tombueng/LuxDMX/docs/display.md

# Design — OLED / TFT status display (issue #5)

Add an **optional on-device display** that shows the gateway's live status without a
browser — IP, universe, frame rate, source count, link quality, and DMX activity —
and **auto-rotates to an alert banner** when something needs attention (two consoles
fighting over the universe, identify, manual override).

> Status: **implemented & committed** on the `hardware` branch (all four firmware envs build).
> Mono bring-up panels ordered: Retoo SH1106 128×64, ARCELI SSD1306 128×64, MakerHawk SSD1306
> 128×32 — covers `dispType 1/2/3`. Colour/SPI path (`dispType 4`) is built but on-hardware
> verification is pending a panel (an SSD1351, or a TFT added per §7 on an existing display).

---

## 1. Displays we support & the graphics library

Two display classes, **one drawing API**:

| Class | Controllers | Bus | Pins | Buffer | Boards |
|---|---|---|---|---|---|
| **Mono OLED** | SSD1306 (128×64, 128×32), SH1106 (128×64) | I²C | 2 | 1 KB | all four |
| **Color OLED** | SSD1351 (128×128 RGB) | SPI | ~5 | 32 KB canvas | esp32 / esp32-s3 only |
| Color TFT *(§7, later)* | ST7735 / ST7789 / ILI9341 | SPI | ~5 | direct-draw | esp32 / esp32-s3 only |

**Library: the [Adafruit_GFX](https://github.com/adafruit/Adafruit-GFX-Library) family**
(not U8g2). Every driver below derives from the common `Adafruit_GFX` base, so the renderer
draws once through a single `Adafruit_GFX*` pointer with `uint16_t` RGB565 colors — monochrome
panels map any non-black color to "pixel on," the SSD1351 shows real color:

```
olikraus/U8g2          ✗  (drives SSD1351 only in monochrome — defeats the color panel)
adafruit/Adafruit GFX Library          ← base class + fonts
adafruit/Adafruit SSD1306              ← SSD1306 mono I²C   (dispType 1,2)
adafruit/Adafruit SH110X               ← SH1106  mono I²C   (dispType 3)  ← Retoo panel
adafruit/Adafruit SSD1351 OLED Library ← SSD1351 color SPI  (dispType 4)  ← DollaTek panel
```

Why this over U8g2: it's the only option that drives **both** the mono I²C OLED *and* a
**full-color** SSD1351 with **one** rendering routine, it opens the §7 color-TFT path for free,
and it matches the Adafruit ecosystem the firmware already uses (`Adafruit_NeoPixel`). Trade-off
vs U8g2: no page-buffer low-RAM mode (mono keeps a 1 KB buffer — fine; we already gate WS push
under 40 KB heap) and a smaller built-in font set (ample for a status screen).

```cpp
Adafruit_GFX* gfx = nullptr;   // draw target: device buffer (mono) or GFXcanvas16 (colour)
// flush: mono -> dispDev->display();  colour -> dispDev->drawRGBBitmap(canvas->getBuffer())
// factory (initDisplay):
//   case 1: gfx = dispDev = new Adafruit_SSD1306(128,64,&Wire,-1); ->begin(...,/*periphBegin*/false);
//   case 3: gfx = dispDev = new Adafruit_SH1106G(128,64,&Wire,-1); ->begin(addr,true);
//   case 4: SPI.begin(sck,-1,mosi,cs); dispDev = new Adafruit_SSD1351(128,128,&SPI,cs,dc,rst);
//           dispDev->begin();  gfx = dispCanvas = new GFXcanvas16(128,128);
```

The per-type `begin()` / flush differences live in the factory; the renderer is type-agnostic.

---

## 2. Pin availability

Mono I²C needs **2 bidirectional GPIOs** (input-only 34–39 can't drive SDA/SCL). Color OLED /
TFT over SPI needs **~5** (SCK, MOSI, CS, DC, RST).

| Board | DMX / LED / EN | Eaten by Ethernet | Free output-capable | Mono I²C | Color SPI |
|---|---|---|---|:--:|:--:|
| `esp32dev` (WROOM) | 16/17, LED 2 | — | 21, 22 (+ many) | ✓ | ✓ (HW SPI 18/23 + CS/DC/RST) |
| `esp32s3dev` | 16/17, LED 48 | — | abundant | ✓ | ✓ |
| `wt32eth01` | 4/5, LED 2 | 0,16,18,19,21,22,23,25,26,27 | **14, 15, 17** only | ✓ | ✗ |
| carrier / `esp32-poe-iso` | 4/36, EN 32, RGB 33 | 0,12,18,19,21,22,23,25,26,27 | 5, 13, 14, 15, 16 | ✓ | ✗ (needs all 5 spares) |

**The color SSD1351 runs on the WiFi dev boards (where bring-up happens), not the Ethernet
boards.** The mono Retoo panel runs everywhere.

**Strapping cautions** (baked into defaults + form help): avoid **GPIO12** (boot-straps flash
voltage; an OLED pull-up can brick boot); **GPIO15** is fine pulled high; on **WT32-ETH01
GPIO16 is the PHY-power pin** — off-limits there.

### Recommended default pins (compile-time `DEF_DISP_*`, overridable in `/config`)

| Board | I²C SDA | I²C SCL |
|---|---|---|
| `esp32dev` | 21 | 22 |
| `esp32s3dev` | 8 | 9 |
| `wt32eth01` | 14 | 15 |
| carrier / `esp32-poe-iso` | 13 | 16 |

Color-SPI pins have no universal default (they're board-specific and only used for `dispType 4`)
— the user sets CS/DC/RST/SCK/MOSI in `/config`. Default `dispType = 0` (**off**) everywhere, so
existing units are unaffected until a user opts in.

---

## Header safety: J4 vs J6

The LuxDMX board has **two** JST SH 1.0 mm 9-pin headers next to each other: **J4** (display) and
**J6** (expansion). Same connector, so a cable physically plugs into either one.

Both headers carry the **same power pins**, and a hard validator
(`hardware/scripts/validate_header_parity.py`) fails the fab export if that ever stops being true:

| pin | J4 — display | J6 — expansion |
|---|---|---|
| **1** | **+3V3** | **+3V3** |
| **2** | **GND** | **GND** |
| 3 | SDA (IO4) | IO35 |
| 4 | SCL (IO5) | IO36 |
| 5 | SCK (IO39) | IO37 |
| 6 | MOSI (IO40) | IO48 |
| 7 | CS (IO41) | TX0 (IO43) |
| 8 | DC (IO42) | RX0 (IO44) |
| 9 | RST (IO38) | GND |

Get it wrong and nothing breaks. The panel still receives correct power; only 3V3 CMOS signals land
in the wrong places, which both sides tolerate. A display plugged into J6 lands its RST on GND, so it
sits harmlessly in reset — dark, but fine. Move it to J4 and it comes up.

**There is no +5V on J6.** Anything needing 5 V gets it from your own supply. That is deliberate:
sharing one power layout across both headers is what makes a swapped cable a non-event, and there
was no free non-strapping GPIO left for a 7th signal anyway (IO3/IO45/IO46 are all strapping), so
pin 9 became a second ground instead.

Labelling the two cables is still worth the ten seconds — a strip of tape saying `DISP` / `EXP` is
what you'll actually read at 2am during a show. And if you only ever use one, **populate only J4**
and leave J6 unfitted.

---

## 3. Config keys

Mirrors how the status LED is wired through the stack (`ledType`/`ledPin`).

| `Config` field | NVS key | `/config` field | Range | Default | Used by |
|---|---|---|---|---|---|
| `dispType` | `disptype` | select | 0=off · 1=SSD1306 128×64 · 2=SSD1306 128×32 · 3=SH1106 128×64 · **4=SSD1351 128×128 color** | `0` | all |
| `dispSda` | `dispsda` | number | −1..48 | `DEF_DISP_SDA` | I²C (1–3) |
| `dispScl` | `dispscl` | number | −1..48 | `DEF_DISP_SCL` | I²C (1–3) |
| `dispRot` | `disprot` | select | 0=normal · 1=flipped 180° | `0` | all |
| `dispCs` | `dispcs` | number | −1..48 | −1 | SPI (4) |
| `dispDc` | `dispdc` | number | −1..48 | −1 | SPI (4) |
| `dispRst` | `disprst` | number | −1..48 | −1 | SPI (4) |
| `dispSck` | `dispsck` | number | −1..48 | −1 | SPI (4) |
| `dispMosi` | `dispmosi` | number | −1..48 | −1 | SPI (4) |

- **I²C address** isn't a field — `initDisplay()` probes `0x3C` then `0x3D` and logs which
  answered. (SSD1351 ignores it.)
- The `/config` "Display" card shows the **I²C pin rows for types 1–3** and the **SPI pin rows
  for type 4**, toggled in JS by the selected type (like `updLedPin()`).
- Touchpoints (all following the LED pattern): `loadConfig` / `saveConfig`, `handleConfigPost`,
  `handleInfoJson`, `src/pages/config.html`.
- **Phase 1 status:** `dispType` (0–3), `dispSda`, `dispScl`, `dispRot` are built and compiling.
  The SPI keys + `dispType 4` are added when color support lands (Phase 2).

---

## 4. Architecture — a `displayTask`, like `ledTask`

The display renders on its **own low-priority FreeRTOS task** (≈4 Hz), exactly like
[`ledTask`](../src/main.cpp). It only **reads** existing state snapshots (`fps`, `senders`,
`netLocalIP()`, `cfg.*`, `hasConflict()`, `manualMode`, `identifyCh`, `dmxBuf`) — never touches
the DMX UART, never blocks `loop()`. A mono I²C flush is ~10–30 ms at 400 kHz; an SSD1351
partial-region redraw over SPI is a few ms — both safely off the DMX path.

```
setup():  loadConfig() → initDisplay() [splash]  →  xTaskCreate(displayTask, "disp", 4096, …, 1)
displayTask():  pick screen (priority, §5) → render via Adafruit_GFX* → flush → delay(250 ms)
```

- `initDisplay()` is a no-op when `dispType == 0`; on probe/begin failure it logs and leaves
  `gfx == nullptr` (no hang — I²C `begin()` NAK-times out; SPI begin always returns).
- Boot sequence on the panel: **"LuxDMX vX.Y.Z"** splash → **"Connecting…"** → status once
  `netConnected()`.
- Color path is **double-buffered**: the renderer draws into a `GFXcanvas16` (32 KB, allocated
  only when `dispType == 4`) and `dispFlush()` blits the whole frame with one `drawRGBBitmap()`.
  The SSD1351 has no RAM buffer, so without this it would visibly flicker — clearing then
  redrawing live on the SPI bus. Mono panels buffer internally, so they flush with `display()`.

---

## 5. Screens — status + auto-rotate

One **status screen** is the resting state. The task switches to a full-screen **alert banner**
while a condition is active, then falls back. No button required.

**Priority (first active wins):** `hasConflict()` → `IDENTIFY` → `manualMode` → status.
Banners dwell ≥1.5 s so a brief blip stays readable.

### 128×64 mono / 128×128 color (8 rows)

Single output (resting):

```
┌────────────────────────────┐
│ LuxDMX           1.0.42  │  title + FIRMWARE_VERSION
│ 192.168.1.50               │  netLocalIP()  — the #1 walk-up info
│ Uni 0    Both              │  output universe + protocol
│ In 33 Out 40 C     Src 1   │  inFpsLive/outFpsLive + style tag
│ WiFi -47dBm         ● LIVE │  link dBm (or "ETH up") + DMX live/idle
└────────────────────────────┘
```

With **both outputs enabled** the universe + FPS rows split into one row per output, each
showing its own universe and its own frame rate (source count moves to the right):

```
┌────────────────────────────┐
│ LuxDMX           1.0.42  │
│ 192.168.1.50               │
│ A U0 44.0fps C             │  output A: universe + out fps + style
│ B U5 43.8fps C      Src 1  │  output B + activeSenderCount()
│ WiFi -47dBm         ● LIVE │
└────────────────────────────┘
```

- Link row: WiFi shows dBm (`netRSSI()`); Ethernet shows `ETH up/down`.
- Universe(s): `dispUniverseLabel()` joins every **enabled** output's universe (`0`, or `0+5`
  for two) in the single-output layout; with two outputs each gets its own `A`/`B` row.
- Per-output FPS: `dispOutFps(i)` is each universe's own 1 s frame rate, and reads `0.0` once
  that input stalls (>1.5 s). The aggregate `fps` still feeds the WebSocket / web UI.
- Rate and style (issue #93): the single-output rows show **In** and **Out** side by side
  rather than one ambiguous `FPS`, because the whole point is whether the two match. A
  trailing `C` or `D` is the transmit style of that port, continuous (free-running at the
  configured rate) or delta (one frame out per frame in). `In 33 Out 40 C` says at a glance
  that this port is resampling a 33.3 fps console onto a 40 fps wire and therefore repeating
  roughly one frame in six.
- Source count: labelled **Sources** (number of active Art-Net / sACN senders), matching the
  `2+ sources` wording on the conflict banner.
- DMX state: `● LIVE` when `millis() - lastDmxMs < 1500` (the LED's threshold), else `idle`.
- **Color panel (SSD1351)** reuses the device's status palette, same language as the status LED:
  title accent + LIVE dot **green** when up (idle *or* live — the LIVE/idle label carries the DMX
  distinction), **orange** when Ethernet is configured but running on the WiFi/AP fallback,
  **blue** during RDM / identify, **red** on no-link; the conflict banner fills **red**. Panel and
  LED always agree.

> **Mono panel color is irrelevant.** White / blue / yellow / yellow-blue panels are all 1 bpp —
> the color is the physical emitter, not addressable. The yellow/blue split panel has a *fixed*
> divide (top 16 px yellow, rest blue) with a small dead gap at y=16; the 64-px layout puts the
> title in y=0..15 (the yellow band) and keeps the first data row at y≥18 so nothing straddles
> the gap. Split panels are 128×64 only.

### 128×32 mono (4 rows)

Title + RSSI bars dropped; live dot moves up beside the IP:

```
┌────────────────────────────┐
│ 10.13.37.2          ● LIVE │
│ U0+5 Both                  │
│ 44.0C/43.8C Src 1          │  per-output out fps + style tag
└────────────────────────────┘
```

The renderer branches on `gfx->height()`, so the same data helpers feed every layout; banners
reuse one centred-text routine with a font chosen by height. **Why size/type is configured, not
detected:** over I²C both heights answer at 0x3C with no resolution read-back, and SPI panels
can't be enumerated at all — so the panel is part of `dispType`, picked in `/config`.

### Controls menu (issue #24)

If a rotary encoder or buttons are wired (see [controls.md](controls.md)), a highest-priority
menu screen takes over the display while you're navigating: a scrolling item list on the tall
panels, or the single selected item on the 128×32 strip. A `>` caret marks the highlight (the
only cue that survives the 1-bit mono collapse), and editing a value wraps it in `<angle
brackets>`. It shows instantly on the first turn and disappears the moment the menu closes.

### Future extra screens (not in v1)

Button-cycled diagnostics — DMX mini-bargraph, RDM device count (`rdmCount`), uptime/heap. The
screen-selector enum is built to extend.

---

## 6. platformio.ini changes

```ini
[env]                       # add to shared lib_deps
lib_deps =
    …
    adafruit/Adafruit GFX Library @ ^1.11.11
    adafruit/Adafruit SSD1306     @ ^2.5.13
    adafruit/Adafruit SH110X      @ ^2.1.12
    adafruit/Adafruit SSD1351 OLED Library @ ^1.3.2

[env:esp32dev]    build_flags = … -DDEF_DISP_SDA=21 -DDEF_DISP_SCL=22
[env:esp32s3dev]  build_flags = … -DDEF_DISP_SDA=8  -DDEF_DISP_SCL=9
[env:wt32eth01]   build_flags = … -DDEF_DISP_SDA=14 -DDEF_DISP_SCL=15
```

`dispType` stays `0` by default in all envs; the user enables the panel from `/config`.

---

## 7. Color TFT — later (esp32 / esp32-s3 only)

Same `Adafruit_GFX*` renderer, additional `dispType` values for `ST7735 160×128` /
`ST7789 240×240` / `ILI9341 320×240` behind their Adafruit drivers, reusing the same SPI pin
config keys from §3. The color SSD1351 work lands most of this — TFT is then just more driver
cases + a larger-font layout. Out of scope for issue #5's first cut.

---

## 8. Verification plan

- **Hardware**: the **Retoo SH1106** on `esp32dev`/`esp32s3dev` (I²C 21/22 or 8/9) → mono path,
  address probe, rotation; the **DollaTek SSD1351** on SPI → color path, status palette; trigger
  the conflict banner by pointing two Art-Net sources at one universe.

---

## 9. Build phases — all implemented

1. ✅ Config plumbing — `Config` fields, NVS, `handleConfigPost`, `handleInfoJson`, `/config`
   "Display" card + JS; `/info.json` round-trips `dispType` + I²C/SPI pins + rotation.
2. ✅ Adafruit_GFX family; `initDisplay()` factory + I²C probe (bails if no panel) + DC-pin guard
   + boot splash; `dispType 4` (SSD1351) with a `GFXcanvas16` double-buffer; per-board `DEF_DISP_*`.
3. ✅ `displayTask()` + status screen (height-aware 128×32 / 128×64 / 128×128 hero layouts).
4. ✅ Auto-rotate banners (conflict / identify / manual) with priority + dwell; colour status palette.
5. ✅ README "Display" section + rendered `display-preview.png`.

**Remaining:** on-hardware bring-up of the mono panels and the colour/SPI path; optional §7 TFT
support (verify colour/SPI on an existing TFT instead of buying an SSD1351).
