tombueng/LuxDMX/web/boards/CREDITS.md

# Board diagram credits

The `/config` pin picker draws a **generated horizontal diagram** for every board
straight from the descriptor's pin data. There are **no third-party image assets** in
this catalog: no board photos and no Fritzing/realistic graphics. Every diagram is our
own SVG, drawn in the browser from the board's GPIO columns.

The GPIO data behind each diagram comes from:

| Board(s) | Source | License |
|---|---|---|
| LuxDMX v6 | the PCB netlist (`hardware/scripts/luxdmx.py`) | project (MIT) |
| ESP32 DevKitC / DevKit v1 / NodeMCU-32S / ESP32-S3 DevKitC-1, Feather / QtPy / XIAO / WT32-ETH01 | hand-tuned published header pinouts in `hardware/scripts/gen_board_descriptor.py` | project (MIT) |
| every other esp32 / esp32s3 board | the arduino-esp32 core `variants/<dir>/pins_arduino.h` (authoritative GPIOs), via `auto_board()` | arduino-esp32 (LGPL-2.1) — data only, not redistributed here |

We only store the extracted GPIO numbers / silk names / flags (facts, extracted by
`hardware/scripts/gen_board_descriptor.py`), never the upstream files themselves.
