tombueng/LuxDMX/docs/rdm-investigation/REPORT.html

# Reliable RDM on the ESP32-S3

An on-the-wire study of RDM timing and DMX-receive reliability on the LuxDMX node

Thomas Büngener

June 2026 (rev 2, July 2026)

Abstract

On-the-wire measurements (a calibrated logic analyzer, N ≥ 20 per result) show the LuxDMX ESP32-S3 node is a reliable RDM (ANSI E1.20) controller: it switches its transceiver to receive about 15 us after sending a request – roughly 160 us before the earliest a compliant fixture may legally reply (176 us) – and catches every response, with WiFi on. WiFi while idle costs nothing; only active web traffic to the device inflates the turnaround, that scales with request rate (not data volume), and even then the worst case stays inside the 176 us budget. A one-line configuration change (moving the web-server task off the CPU core that runs RDM) is flashed and verified, and nearly doubles the worst-case safety margin (58 to 101 us). A wired-Ethernet cross-check then exposed a regression: enabling the W5500 SPI-Ethernet interface made RDM discovery fail about 93 % of the time (1 of 15, vs 15 of 15 on WiFi), because the W5500 driver starved the same interrupt that performs the turnaround. A blunt interrupt-priority bump was tried and disproven (it crashes the W5500 bring-up); the fix that works is core isolation, running the W5500 and the web/TCP task on core 0 and leaving DMX/RDM on core 1. On-device instrumentation then confirmed it: 800 discoveries over the wired interface at 100 % steady-state success. Over WiFi and over the wired interface, RDM is reliable.

All timing is measured on the physical RS485 wire with a calibrated logic analyzer (§4); every quantitative claim is N ≥ 20 with a stated confidence level. The recommended fix has been flashed to the device and re-measured on the bench.

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

## Management summary

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

## 1. Question

Two questions drive this study:

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

## 2. Test setup (hardware-in-the-loop bench)

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

LA taps (common ground with both boards):

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

## 3. The logic analyzer (and why a custom one)

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

## 4. Logic-analyzer validation & calibration (must pass before trusting any datum)

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

Time base — result (HIGH confidence):

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

## 5. Methodology

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

## 6. Results — LuxDMX RDM capabilities

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

Figure 1 — one full RDM discovery transaction on the wire. ctrlTX (the request) ends ~988 µs; the controller flips EN to receive ~12 µs later (orange); the responder replies at ~1614 µs and the controller receives it at the same instant (ctrlRX green = simTX red), decoded as 7×0xFE preamble + mask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

Figure 2 — controller TX→RX turnaround vs network load (N ≥ 25 per condition; WiFi present in all but the first group). WiFi-off and WiFi-on-idle are indistinguishable (~16 vs ~15 µs median), so the radio being on costs nothing; only active web traffic inflates the turnaround, and it scales with r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

6.3 Capability matrix.

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

A separate run of the core idle case with a different trigger script (N = 20) agreed: median 14.6, mean 15.7, min 0.2, max 41.0 µs. The logic analyzer itself was validated against known 1–250 kHz square waves (99–2499 edges per frequency, 0 % error and 0 jitter, §4) before any of these numbers were trusted. Every measured maximum, in every condition, stays below the 176 µs RESPONDER_MIN — that is the core reliability result, and it is a property of the whole distribution, not just the median.

6.5 Does the number of fixtures matter? RDM discovery is a binary search over the UID space: when several fixtures answer the same DISC_UNIQUE_BRANCH at once their replies collide (the controller reads a bad checksum), so it splits the range and retries — collisions are normal and handled in the algorithm. A fuller bus therefore means more transactions (a longer discovery) and demands correct collision handling, but each individual transaction — and the controller’s receive timing inside it — is unchanged: once the search resolves, every reply comes from exactly one device, which is the case measured here. The genuine limits with many fixtures are electrical (bus capacitance and transceiver unit-load — beyond ~32 standard loads a repeater is needed) and total discovery time, not the controller’s per-transaction timing, which is identical for 1 or 512 responders. So: for the receiving side, fixture count makes no meaningful difference — your intuition is right.

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

## 7. Root-cause analysis

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

## 8. Fix — flashed and measured

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

## 9. Answer to the forum question (ESP32 DMX-receive quirks)

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

Receive failure modes, measured (~2,100 frames / 60 s each). Only blocking interrupts past the 5.6 ms FIFO budget corrupts receive (~13x baseline). Real flash writes during receive do not, because esp_dmx’s IRAM ISR runs through the cache blackout; a driver without an IRAM ISR would corrupt here j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

## 10. Cross-validation, limitations, next steps

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

## 11. Update (rev 2): RMT-DMX and the esp_dmx-free RDM path

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

### 11.1 Why a structural fix

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

The fix that removes the dependency is to stop timing DMX from an ISR at all.

### 11.2 RMT-DMX (transmit)

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

### 11.3 esp_dmx-free RDM

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

### 11.4 Validated on real ESP32-S3 silicon

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

### 11.5 Crash-hardening found under stress

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

### 11.6 What this changes, and what it does not

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

## Appendix A. LA firmware (s3-logic-analyzer) · B. la_analyze.py · C. raw captures + figures

(listings attached in the repo; figures/hr05_timing.png is the reference transaction.)
