tombueng/LuxDMX/docs/rdm-investigation/figures/bench_diagram.pdf

# Hardware-in-the-loop bench

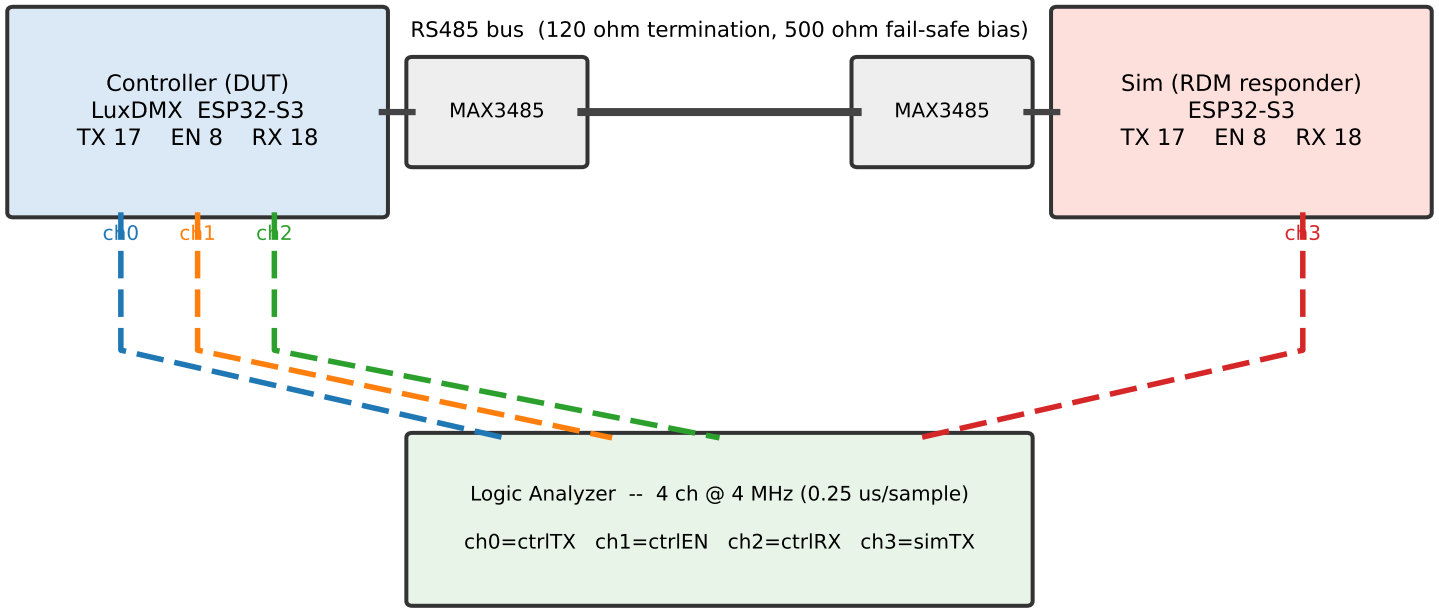
[picture p20: figure]
Controller (DUT) LuxDMX ESP32-S3; Sim (RDM responder) ESP32-S3; MAX3485; ch0=ctrlTX ch1=ctrlEN ch2=ctrlRX ch3=simTX

Logic Analyzer -- 4 ch @ 4 MHz (0.25 us/sample)

RS485 bus (120 ohm termination, 500 ohm fail-safe bias)

common ground across all three boards
