tombueng/LuxDMX/docs/rdm-investigation/figures/dmx_rx_budget.pdf

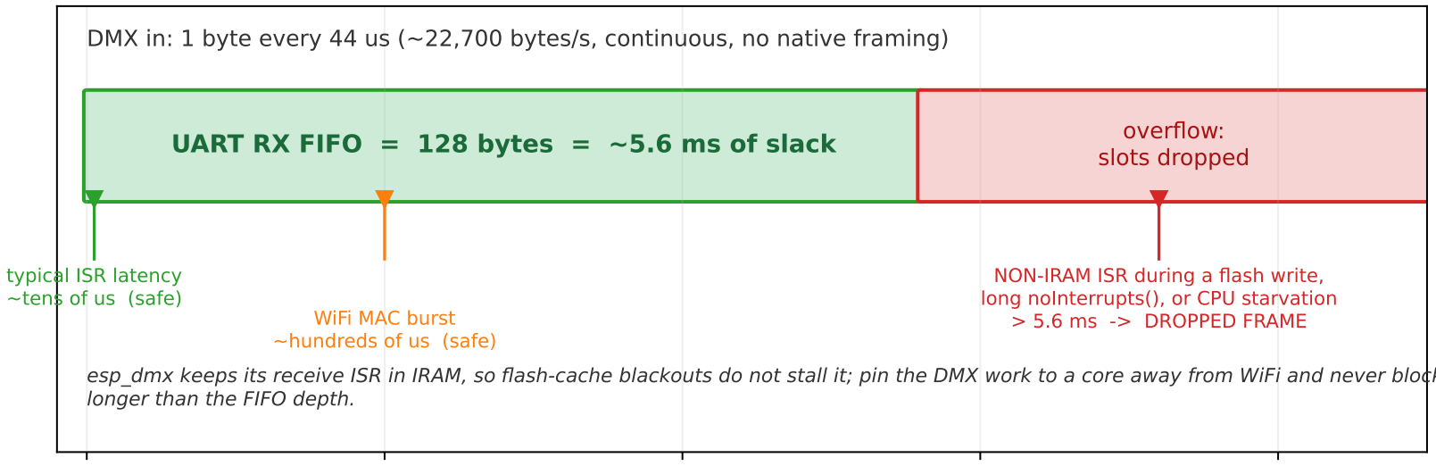
[picture p21: figure]
slots dropped; typical ISR latency; ~tens of; us (safe); WiFi MAC burst; ~hundreds; of us (safe); NON-IRAM ISR during a flash write,; long noInterrupts(), or CPU starvation > 5.6 ms -> DROPPED FRAME; longer than the FIFO depth.

0 | 2 | 4 | 6 | 8
| | time the receive ISR is delayed (ms)
UART RX FIFO = 128 bytes = ~5.6 | ms of slack | overflow:

### DMX in: 1 byte every 44 us (~22,700 bytes/s, continuous, no native framing)

esp_dmx keeps its receive ISR | in IRAM, so flash-cache blackouts do not stall it; pin the DMX | work to a core away from WiFi and never block interrupts

## Why ESP32 DMX receive works, and the only way it breaks: the interrupt-latency budget
