tombueng/LuxDMX/docs/rdm-investigation/figures/dmx_rx_failmodes.pdf

baseline
(no WiFi)

interrupts blocked
8 ms > 5.6 ms FIFO

flash writes

during receive
(esp_dmx IRAM ISR)

0

5

10

15

20

25

30

### framing / overrun errors (60 s run)

2 errors | 3 errors
in 2196 frames | in 2059 frames

### 25 errors in 2108 frames

Deliberately blocking interrupts for 8 ms (> the 5.6 ms FIFO) corrupts receive (~13x baseline).
Real flash writes during receive do NOT: esp_dmx keeps its ISR in IRAM and runs through the cache

blackout. A DMX library WITHOUT an IRAM ISR would corrupt here exactly like the blocked-ISR case.

## What breaks ESP32 DMX receive: an interrupt stall past the FIFO budget
