tombueng/LuxDMX/docs/rdm-investigation/figures/dmx_rx_reliability.pdf

0 | 2000 | 4000 | 6000 | 8000 | 10000
DMX frames (ESP32-S3 + esp_dmx receiver, WiFi OFF, on the RS485 wire)

## 10157 frames received

0 errors

### DMX receive integrity: 10157 frames, 0 errors (0.00% loss)
