tombueng/LuxDMX/docs/rdm-investigation/figures/dmx_rx_wifi.pdf

### no WiFi DMX ISR core 1

### WiFi active DMX ISR core 0

### WiFi active DMX ISR core 1

0

1

2

3

4

5

6

### framing / overrun errors (90 s run)

### 0 errors in 3246 frames

### 1 error in 3162 frames

### 0 errors in 3135 frames

WiFi-scan load on core 0 throughout B and C. The 128-byte UART FIFO + IRAM ISR absorb the WiFi-MAC interrupt latency: ~0 corrupted frames whether the DMX receive ISR shares the WiFi core (B) or is isolated (C). (Frame *gaps* in all three are the gateway source's own output jitter, present without WiFi too, not a receiver effect.)

## WiFi load does not corrupt ESP32-S3 esp_dmx receive
