tombueng/LuxDMX/docs/rdm-investigation/figures/eth_vs_wifi_rdm.pdf

WiFi | Wired Ethernet (W5500 active)

0

20

40

60

80

100

RDM discovery success rate (%)

15 / 15

1 / 15

RDM discovery: WiFi vs W5500 wired Ethernet same node, same bus, same responder
