tombueng/LuxDMX/docs/rdm-investigation/figures/hr05_timing.pdf

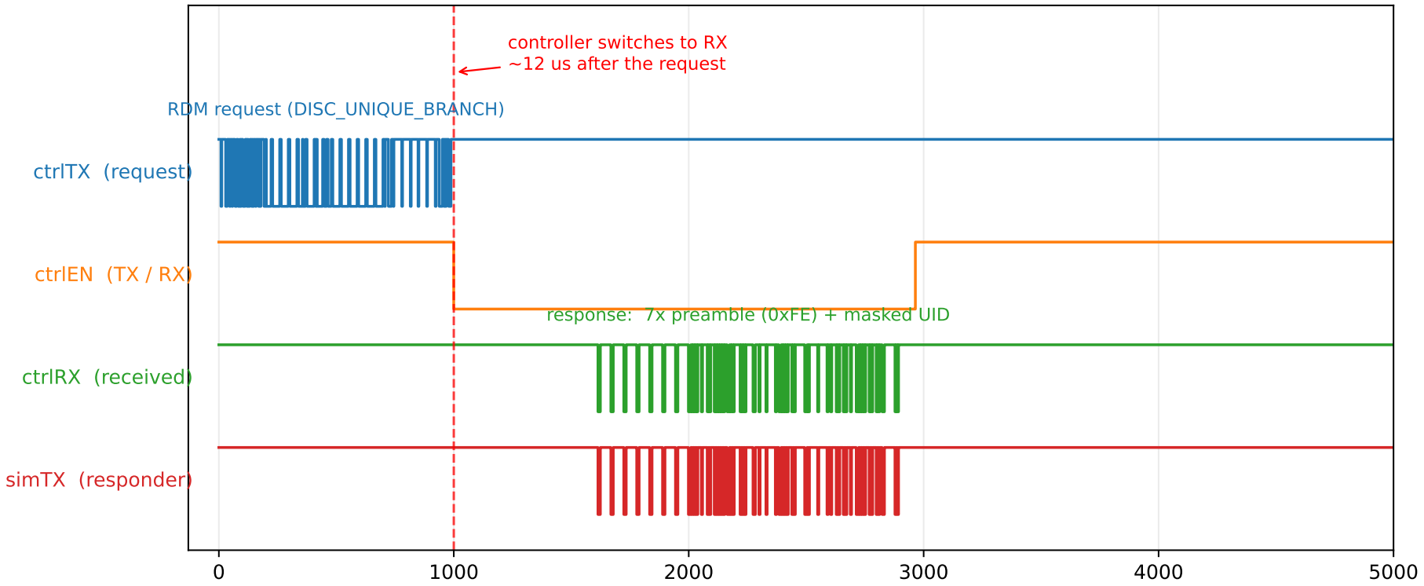
[picture p22: figure]
ctrlTX (request); ctrlEN (TX / RX); ctrlRX (received); simTX (responder); controller switches to RX ~12 us after the request; RDM request (DISC_UNIQUE_BRANCH)

time (us) [logic analyzer @ 4 MHz, 0.25 us/sample] response: 7x preamble (0xFE) + masked UID

### One full RDM discovery transaction on the RS485 wire
