tombueng/LuxDMX/docs/rdm-investigation/figures/wifi_turnaround.pdf

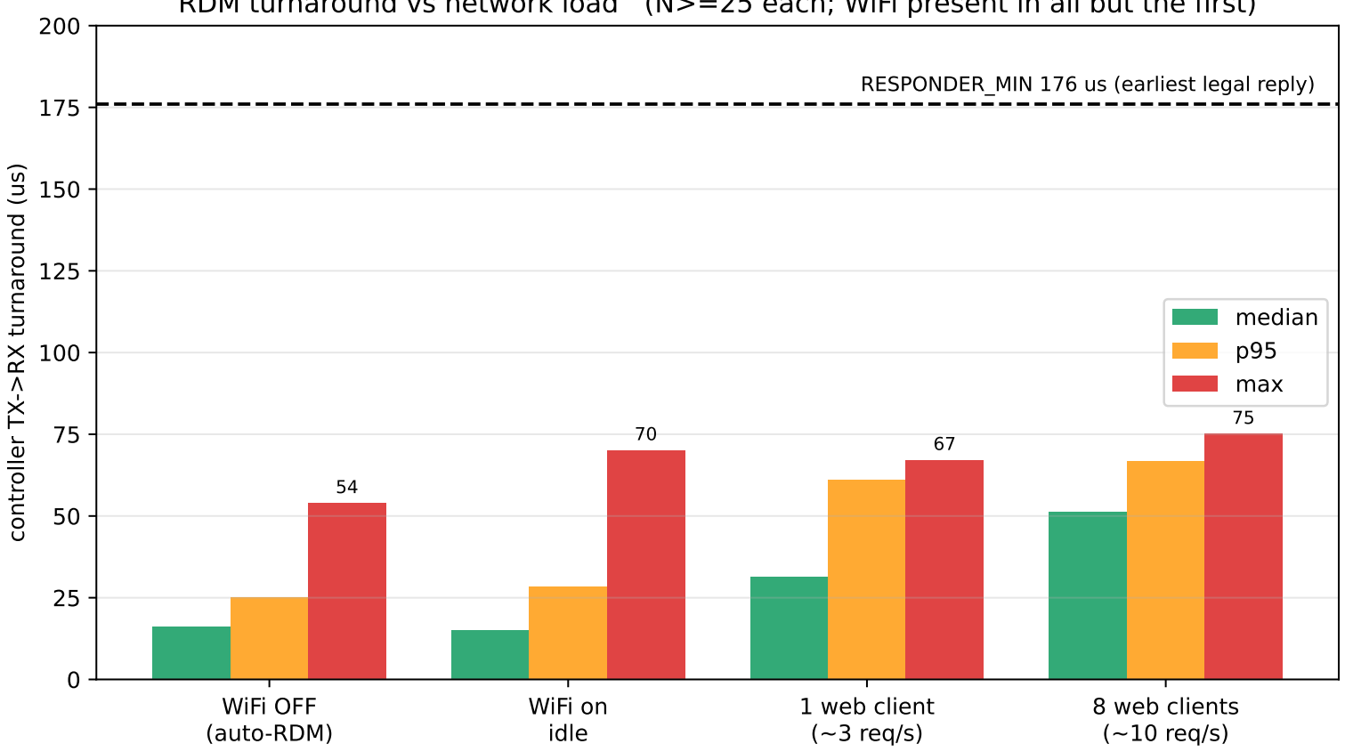
[picture p23: figure]
WiFi OFF (auto-RDM); WiFi on idle; 1 web client (~3 req/s); 8 web clients (~10 req/s); controller TX->RX turnaround (us); median p95 max

RESPONDER_MIN 176 us (earliest legal reply)

### RDM turnaround vs network load (N>=25 each; WiFi present in all but the first)
