tombueng/LuxDMX/docs/mock2.png

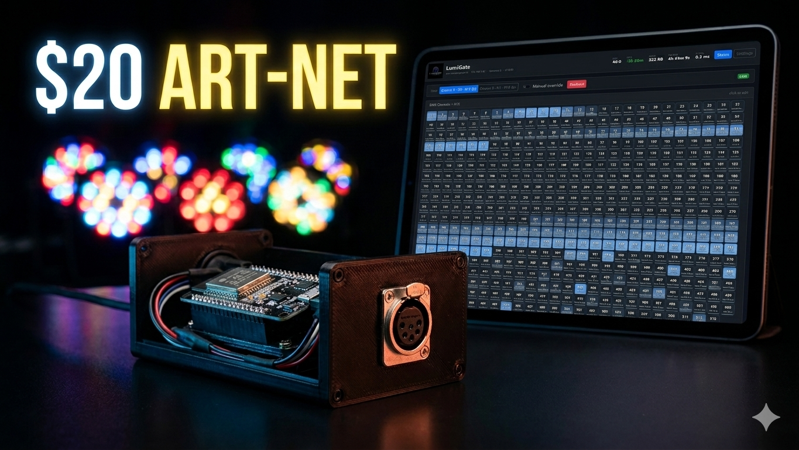
docs/mock2.png
