tombueng/LuxDMX/docs/mock3.png

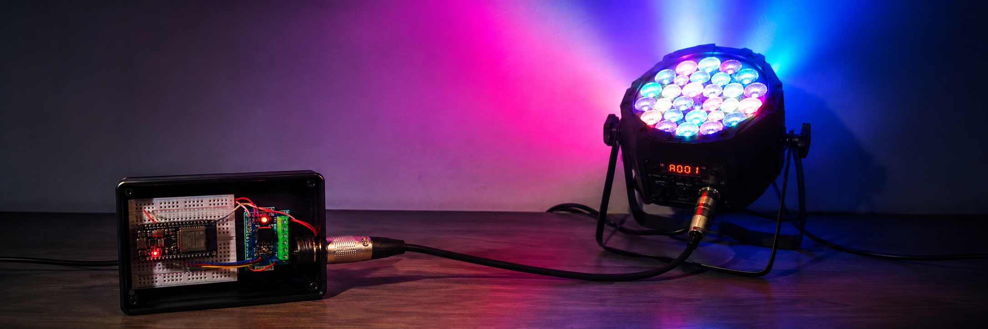
docs/mock3.png
