tombueng/LuxDMX/docs/mock4.png

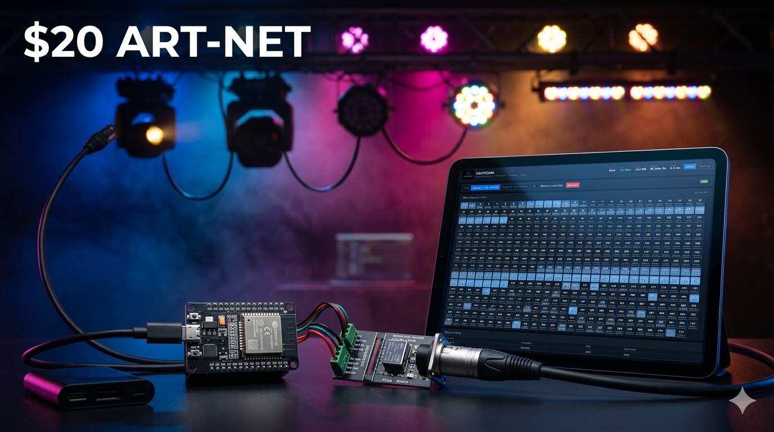
docs/mock4.png
