tombueng/LuxDMX/docs/mock5.png

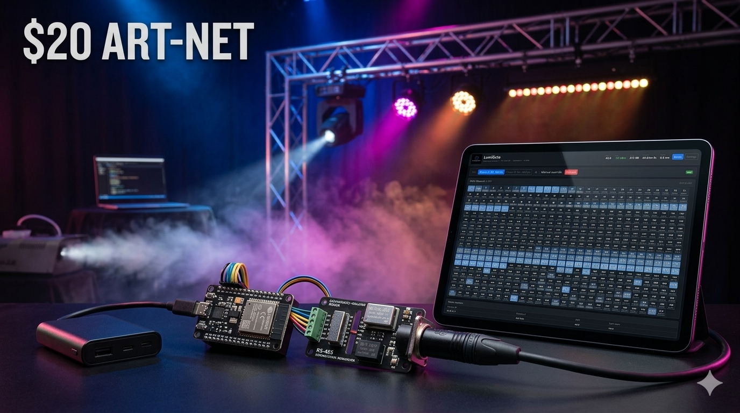
docs/mock5.png
