tombueng/LuxDMX/docs/mock6.png

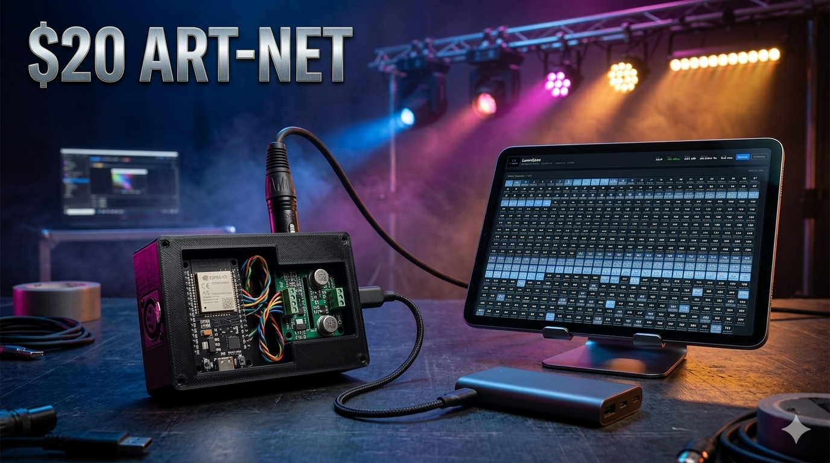
docs/mock6.png
