tombueng/LuxDMX/docs/rdm-investigation/figures/dmx_rx_budget.png

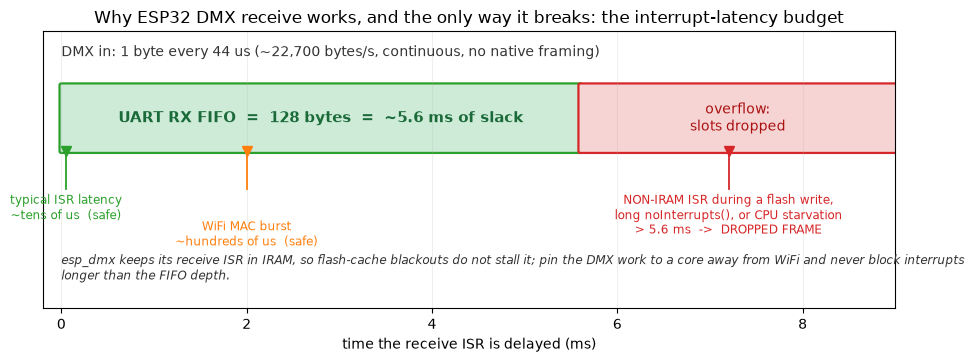
docs/rdm-investigation/figures/dmx_rx_budget.png
