tombueng/LuxDMX/docs/social-preview.jpg

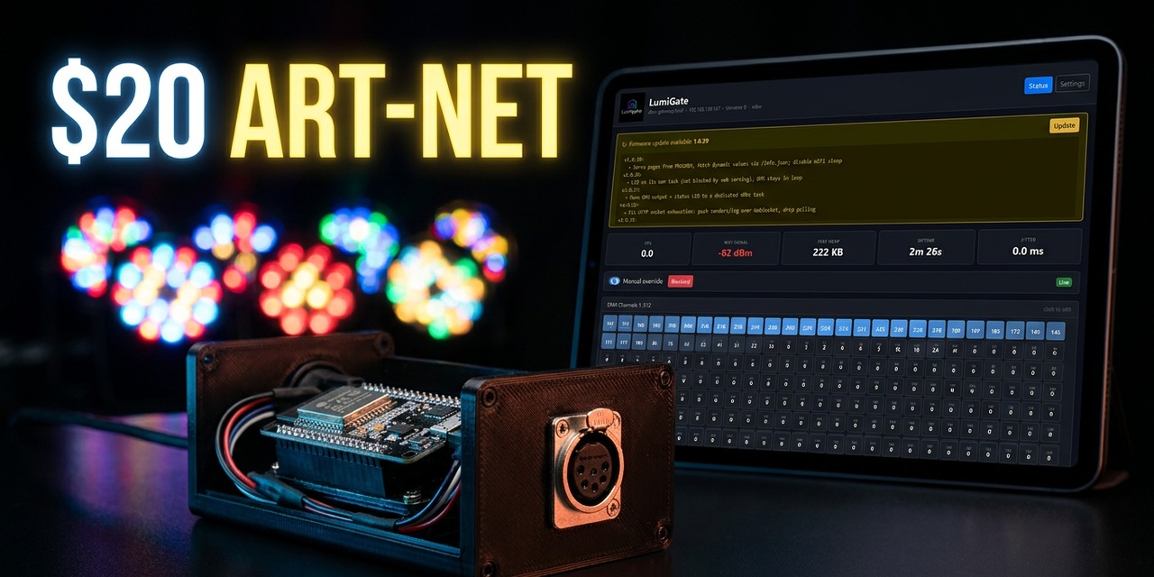
docs/social-preview.jpg
