tombueng/LuxDMX/hardware/luxdmx.py

#!/usr/bin/env python
"""LuxDMX v5 — standalone ESP32-S3 Art-Net/sACN -> isolated DMX gateway (SKiDL).

Self-contained board (no plug-in module):
  ESP32-S3-WROOM-1-N8  +  W5500 SPI-Ethernet + HR911105A MagJack
  CH340K USB-UART (auto-reset) on a USB-C (data) inlet  +  SY8089 5V->3.3V buck
  Isolated DMX out: CA-IS3082W + B0505S iso-DC-DC + XLR-3 (+ SM712 TVS, 120R term)
  5 status LEDs (red/green/yellow/blue/white) direct on GPIOs

Pin map (ESP32-S3): SPI SCLK=IO12 MOSI=IO11 MISO=IO13 CS=IO10 INT=IO14 ETHRST=IO9;
  DMX DI=IO17 RO=IO18 DE=IO8; LEDs R=IO1 G=IO2 Y=IO6 B=IO7 W=IO15; UART0 TX=IO43 RX=IO44.

NB: the W5500<->MagJack analog section (TX/RX pairs, center-tap/TOCAP) follows the WIZnet
reference; verify against the W5500 datasheet + HR911105A before fabricating.

Regenerate:  python luxdmx.py   -> luxdmx.net
"""
import os
from skidl import Part, Pin, Net, TEMPLATE, SKIDL, generate_netlist, ERC, set_default_tool, KICAD9

set_default_tool(KICAD9)
PT = Pin.types
HERE = os.path.dirname(os.path.abspath(__file__))


def mk(name, prefix, fp, pins, value=None):
    t = Part(tool=SKIDL, name=name, ref_prefix=prefix, dest=TEMPLATE)
    for num, pname, func in pins:
        t += Pin(num=str(num), name=pname, func=func)
    t.footprint = fp
    if value:
        t.value = value
    return t


def two(name, prefix, fp, value):
    return mk(name, prefix, fp, [(1, '1', PT.PASSIVE), (2, '2', PT.PASSIVE)], value)()


def R(ref, val, fp='Resistor_SMD:R_0402_1005Metric'):
    r = two('R', 'R', fp, val); r.ref = ref; return r


def C(ref, val, fp='Capacitor_SMD:C_0402_1005Metric'):
    c = two('C', 'C', fp, val); c.ref = ref; return c


# ---- Nets -------------------------------------------------------------------
P5V = Net('+5V'); P3V3 = Net('+3V3'); GND = Net('GND')
# Power-input OR-ing + PoE
P5V_USB = Net('+5V_USB'); P5V_POE = Net('+5V_POE')             # the two diode-OR sources -> P5V rail
VPOE_P = Net('VPOE+'); VPOE_N = Net('VPOE-')                   # rectified PoE 37-57V from the magjack (isolated from board GND by the PD module)
VISO = Net('VISO'); GND2 = Net('GNDISO')                       # isolated DMX bus side
USB_DP = Net('USB_DP'); USB_DM = Net('USB_DM'); CC1 = Net('CC1'); CC2 = Net('CC2')
S3_TX = Net('S3_TX'); S3_RX = Net('S3_RX')                     # UART0 console/flash
EN = Net('EN'); IO0 = Net('IO0'); DTR = Net('DTR'); RTS = Net('RTS')
SCLK = Net('SCLK'); MOSI = Net('MOSI'); MISO = Net('MISO')
ETH_CS = Net('ETH_CS'); ETH_INT = Net('ETH_INT'); ETH_RST = Net('ETH_RST')
DMX_TX = Net('DMX_TX'); DMX_RX = Net('DMX_RX'); DMX_EN = Net('DMX_EN')
DMX_A = Net('DMX_A'); DMX_B = Net('DMX_B')
# --- 2nd isolated DMX universe (its own galvanic island: VISO2 / GNDISO2) ---
VISO2 = Net('VISO2'); GNDI2 = Net('GNDISO2')                   # 2nd isolated DMX bus side
DMX2_TX = Net('DMX2_TX'); DMX2_RX = Net('DMX2_RX'); DMX2_EN = Net('DMX2_EN')
DMX2_A = Net('DMX2_A'); DMX2_B = Net('DMX2_B')
# --- ruggedization (harsh-environment hardening): cable-side DMX nets (after the CM chokes),
#     fused/filtered power rails. See VALIDATION.md "Ruggedization" + docs/ruggedization.md ---
DMX_AO = Net('DMX_AO'); DMX_BO = Net('DMX_BO')            # DMX1 after L2 common-mode choke (SM712/choke node)
DMX2_AO = Net('DMX2_AO'); DMX2_BO = Net('DMX2_BO')        # DMX2 after L3 common-mode choke
# DMX512-A Protected (Annex C): cable/XLR side of the per-line series PTC. cable -> DMX_*X -> PTC -> DMX_*O (SM712)
DMX_AX = Net('DMX_AX'); DMX_BX = Net('DMX_BX')            # DMX1 XLR/breakout side of F2/F3 PTC
DMX2_AX = Net('DMX2_AX'); DMX2_BX = Net('DMX2_BX')        # DMX2 XLR/breakout side of F4/F5 PTC
P5V_USBF = Net('+5V_USBF')                                # USB VBUS after F1 PTC resettable fuse
P5V_DMX = Net('+5V_DMX')                                  # +5V after FB1 ferrite -> isolated DMX DC-DC inputs
VISO_DRV = Net('VISO_DRV'); VISO2_DRV = Net('VISO2_DRV')  # DMX-driver supply after FB2/FB3 ferrite
LED_R = Net('LED_R'); LED_G = Net('LED_G'); LED_Y = Net('LED_Y'); LED_B = Net('LED_B'); LED_W = Net('LED_W')
# W5500 analog / Ethernet
XI = Net('XI'); XO = Net('XO'); V12 = Net('W5500_1V2'); TOCAP = Net('TOCAP')
ETH_TXP = Net('ETH_TXP'); ETH_TXN = Net('ETH_TXN'); ETH_RXP = Net('ETH_RXP'); ETH_RXN = Net('ETH_RXN')
ETH_TCT = Net('ETH_TCT'); ETH_RCT = Net('ETH_RCT'); ETH_LL = Net('ETH_LINKLED'); ETH_AL = Net('ETH_ACTLED')
LX = Net('BUCK_LX'); FB = Net('BUCK_FB')

# ============================================================================
# U1  ESP32-S3-WROOM-1-N8  (module)
# ============================================================================
S3 = mk('ESP32-S3-WROOM-1-N8', 'U', 'RF_Module:ESP32-S3-WROOM-1',
        [(1, 'GND', PT.PWRIN), (2, '3V3', PT.PWRIN), (3, 'EN', PT.INPUT),
         (4, 'IO4', PT.BIDIR), (5, 'IO5', PT.BIDIR), (6, 'IO6', PT.BIDIR), (7, 'IO7', PT.BIDIR),
         (8, 'IO15', PT.BIDIR), (9, 'IO16', PT.BIDIR), (10, 'IO17', PT.BIDIR), (11, 'IO18', PT.BIDIR),
         (12, 'IO8', PT.BIDIR), (13, 'IO19', PT.BIDIR), (14, 'IO20', PT.BIDIR), (15, 'IO3', PT.BIDIR),
         (16, 'IO46', PT.BIDIR), (17, 'IO9', PT.BIDIR), (18, 'IO10', PT.BIDIR), (19, 'IO11', PT.BIDIR),
         (20, 'IO12', PT.BIDIR), (21, 'IO13', PT.BIDIR), (22, 'IO14', PT.BIDIR), (23, 'IO21', PT.BIDIR),
         (24, 'IO47', PT.BIDIR), (25, 'IO48', PT.BIDIR), (26, 'IO45', PT.BIDIR), (27, 'IO0', PT.BIDIR),
         (28, 'IO35', PT.BIDIR), (29, 'IO36', PT.BIDIR), (30, 'IO37', PT.BIDIR), (31, 'IO38', PT.BIDIR),
         (32, 'IO39', PT.BIDIR), (33, 'IO40', PT.BIDIR), (34, 'IO41', PT.BIDIR), (35, 'IO42', PT.BIDIR),
         (36, 'RXD0', PT.BIDIR), (37, 'TXD0', PT.BIDIR), (38, 'IO2', PT.BIDIR), (39, 'IO1', PT.BIDIR),
         (40, 'GND', PT.PWRIN), (41, 'EP', PT.PWRIN)], value='ESP32-S3-WROOM-1-N8')
U1 = S3(); U1.ref = 'U1'
U1['GND'] += GND; U1[40] += GND; U1['EP'] += GND
U1['3V3'] += P3V3
U1['EN'] += EN
U1['IO0'] += IO0
U1['TXD0'] += S3_TX; U1['RXD0'] += S3_RX
# SPI -> W5500
U1['IO12'] += SCLK; U1['IO11'] += MOSI; U1['IO13'] += MISO
U1['IO10'] += ETH_CS; U1['IO14'] += ETH_INT; U1['IO9'] += ETH_RST
# DMX universe 1 (UART/port 1)
U1['IO17'] += DMX_TX; U1['IO18'] += DMX_RX; U1['IO8'] += DMX_EN
# DMX universe 2 (UART/port 2): TX=IO16  RX=IO21  DE/nRE=IO47  (set in /config: out#2 tx16 rx21 rts47)
U1['IO16'] += DMX2_TX; U1['IO21'] += DMX2_RX; U1['IO47'] += DMX2_EN
# LEDs
U1['IO1'] += LED_R; U1['IO2'] += LED_G; U1['IO6'] += LED_Y; U1['IO7'] += LED_B; U1['IO15'] += LED_W
# module decoupling
Cs1 = C('C1', '100nF'); Cs1[1] += P3V3; Cs1[2] += GND
Cs2 = C('C2', '10uF', 'Capacitor_SMD:C_0805_2012Metric'); Cs2[1] += P3V3; Cs2[2] += GND
# EN reset RC + BOOT/EN pull-ups
Ren = R('R1', '10k'); Ren[1] += P3V3; Ren[2] += EN
Cen = C('C3', '1uF'); Cen[1] += EN; Cen[2] += GND   # EN power-on RC: 10k x 1uF = 10ms ramp (Espressif ref; was 100nF=1ms, marginal)
Rb = R('R2', '10k'); Rb[1] += P3V3; Rb[2] += IO0
SWb = mk('SW_PUSH', 'SW', 'Button_Switch_SMD:SW_SPST_B3U-1000P',
         [(1, '1', PT.PASSIVE), (2, '2', PT.PASSIVE)], value='BOOT')
SW1 = SWb(); SW1.ref = 'SW1'; SW1[1] += IO0; SW1[2] += GND
SW2 = SWb(); SW2.ref = 'SW2'; SW2.value = 'RST'; SW2[1] += EN; SW2[2] += GND

# ============================================================================
# U2  W5500 SPI Ethernet  + Y1 25MHz + magjack
# ============================================================================
W5 = mk('W5500', 'U', 'C32843:LQFP-48_L7.0-W7.0-P0.50-LS9.0-BL',
        [(1, 'TXN', PT.PASSIVE), (2, 'TXP', PT.PASSIVE), (3, 'AGND', PT.PWRIN), (4, 'AVDD', PT.PWRIN),
         (5, 'RXN', PT.PASSIVE), (6, 'RXP', PT.PASSIVE), (7, 'DNC', PT.NOCONNECT), (8, 'AVDD', PT.PWRIN),
         (9, 'AGND', PT.PWRIN), (10, 'EXRES1', PT.PASSIVE), (11, 'AVDD', PT.PWRIN), (12, 'NC', PT.NOCONNECT),
         (13, 'NC', PT.NOCONNECT), (14, 'AGND', PT.PWRIN), (15, 'AVDD', PT.PWRIN), (16, 'AGND', PT.PWRIN),
         (17, 'AVDD', PT.PWRIN), (18, 'VBG', PT.PASSIVE), (19, 'AGND', PT.PWRIN), (20, 'TOCAP', PT.PASSIVE),
         (21, 'AVDD', PT.PWRIN), (22, '1V2O', PT.PWROUT), (23, 'RSVD', PT.NOCONNECT), (24, 'SPDLED', PT.OUTPUT),
         (25, 'LINKLED', PT.OUTPUT), (26, 'DUPLED', PT.OUTPUT), (27, 'ACTLED', PT.OUTPUT), (28, 'VDD', PT.PWRIN),
         (29, 'GND', PT.PWRIN), (30, 'XI', PT.INPUT), (31, 'XO', PT.OUTPUT), (32, 'SCSn', PT.INPUT),
         (33, 'SCLK', PT.INPUT), (34, 'MISO', PT.OUTPUT), (35, 'MOSI', PT.INPUT), (36, 'INTn', PT.OUTPUT),
         (37, 'RSTn', PT.INPUT), (38, 'RSVD', PT.NOCONNECT), (39, 'RSVD', PT.NOCONNECT), (40, 'RSVD', PT.NOCONNECT),
         (41, 'RSVD', PT.NOCONNECT), (42, 'RSVD', PT.NOCONNECT), (43, 'PMODE2', PT.INPUT), (44, 'PMODE1', PT.INPUT),
         (45, 'PMODE0', PT.INPUT), (46, 'NC', PT.NOCONNECT), (47, 'NC', PT.NOCONNECT), (48, 'AGND', PT.PWRIN)],
        value='W5500')
U2 = W5(); U2.ref = 'U2'
for n in (3, 9, 14, 16, 19, 48):
    U2[n] += GND          # AGND
U2['GND'] += GND
for n in (4, 8, 11, 15, 17, 21):
    U2[n] += P3V3         # AVDD
U2['VDD'] += P3V3
U2['SCLK'] += SCLK; U2['MOSI'] += MOSI; U2['MISO'] += MISO
U2['SCSn'] += ETH_CS; U2['INTn'] += ETH_INT; U2['RSTn'] += ETH_RST
U2['XI'] += XI; U2['XO'] += XO
U2['1V2O'] += V12; U2['TOCAP'] += TOCAP
U2['TXP'] += ETH_TXP; U2['TXN'] += ETH_TXN; U2['RXP'] += ETH_RXP; U2['RXN'] += ETH_RXN
U2['LINKLED'] += ETH_LL; U2['ACTLED'] += ETH_AL
# PMODE0..2 left to internal pull-ups (all-capable auto-negotiation)
# W5500 support parts
Rset = R('R3', '12.4k'); Rset[1] += U2['EXRES1']; Rset[2] += GND      # W5500 EXRES1: datasheet 12.4k 1% (was 12k -3.2%, on-spec now)
C12a = C('C4', '1uF'); C12a[1] += V12; C12a[2] += GND
C12b = C('C5', '100nF'); C12b[1] += V12; C12b[2] += GND
Ctoc = C('C6', '4.7uF'); Ctoc[1] += TOCAP; Ctoc[2] += GND             # TOCAP ~4.7uF (datasheet)
# VBG (pin 18): left floating per W5500 datasheet (no cap)
for i, ref in enumerate(['C8', 'C9', 'C10', 'C11']):
    cc = C(ref, '100nF'); cc[1] += P3V3; cc[2] += GND                  # AVDD/VDD decoupling
# 25 MHz crystal
XT = mk('Crystal', 'Y', 'Crystal:Crystal_SMD_2520-4Pin_2.5x2.0mm',
        [(1, '1', PT.PASSIVE), (2, '2', PT.PASSIVE), (3, '3', PT.PASSIVE), (4, '4', PT.PASSIVE)],
        value='25MHz')
Y1 = XT(); Y1.ref = 'Y1'
Y1[1] += XI; Y1[3] += XO; Y1[2] += GND; Y1[4] += GND
# crystal C2981624 is CL=9pF (2520-25-9; the CL=20pF C2981622 kept going OOS at JLC; C2981624 is in stock).
# CL=(C1*C2)/(C1+C2)+Cstray; 10pF || 10pF + ~4pF stray = 9pF, matching the 9pF crystal. C0G/NP0 required.
# NOTE: a mainstream 3225 package (C9006, JLC Basic 247k) would be the durable "always-available" fix, but the
# 2520->3225 footprint swap needs a supervised re-route of the packed W5500 crystal corner (deferred).
Cx1 = C('C12', '10pF C0G'); Cx1[1] += XI; Cx1[2] += GND
Cx2 = C('C13', '10pF C0G'); Cx2[1] += XO; Cx2[2] += GND
# MagJack HY931147C (C91754) — THT 10/100 PoE magjack: integrated magnetics + an INTEGRATED
# PoE rectifier (Mode A+B bridge -> V+ pin9 / V- pin10) + 2 LEDs. Replaces the non-PoE
# HR961160C: the internal bridge does the rectification, so no external BR1/BR2 are needed.
# NB pin->function map is per the HY931147C datasheet (pulled via easyeda2kicad C91754):
#   1=RD- 2=RD+ 3=RX-CT 4=TX-CT 5=TD- 6=TD+ 7/8=NC 9=V+ 10=V- 11/12=LED-Y 13/14=LED-G.
#   VERIFIED against HanRun datasheet REV.A/1 (2026-06-22): pin/function map, TX<->RX pairing
#   (chip-side TD=5/6, RD=1/2; straight MDI, matters since W5500 has no auto-MDIX) and LED polarity
#   (anodes 11/13, cathodes 12/14) all confirmed. Within-pair +/- is polarity-tolerant.
MJ = mk('HY931147C', 'J', 'C91754:RJ45-TH_HY931147C',
        [(1, 'RDN', PT.PASSIVE), (2, 'RDP', PT.PASSIVE), (3, 'RCT', PT.PASSIVE), (4, 'TCT', PT.PASSIVE),
         (5, 'TDN', PT.PASSIVE), (6, 'TDP', PT.PASSIVE), (7, 'NC', PT.NOCONNECT), (8, 'NC', PT.NOCONNECT),
         (9, 'POE_VP', PT.PASSIVE), (10, 'POE_VN', PT.PASSIVE),
         (11, 'LEDYA', PT.PASSIVE), (12, 'LEDYK', PT.PASSIVE), (13, 'LEDGA', PT.PASSIVE), (14, 'LEDGK', PT.PASSIVE),
         ('GND1', 'SH', PT.PASSIVE), ('GND2', 'SH', PT.PASSIVE)], value='HY931147C')
J3 = MJ(); J3.ref = 'J3'
J3['TDP'] += ETH_TXP; J3['TDN'] += ETH_TXN; J3['RDP'] += ETH_RXP; J3['RDN'] += ETH_RXN
# W5500 TX=current-mode -> chip-side TX-CT(pin4) biased to 3V3 via 49.9R; RX-CT(pin3) to GND via cap (WIZnet ref)
J3['TCT'] += ETH_TCT; J3['RCT'] += ETH_RCT
Rtct = R('R18', '49.9R'); Rtct[1] += ETH_TCT; Rtct[2] += P3V3
Ctct = C('C14', '100nF'); Ctct[1] += ETH_TCT; Ctct[2] += GND
Crct = C('C22', '100nF'); Crct[1] += ETH_RCT; Crct[2] += GND
J3['POE_VP'] += VPOE_P; J3['POE_VN'] += VPOE_N     # integrated-rectifier PoE DC out -> DP9900M VIN+/VIN-
J3['GND1'] += GND; J3['GND2'] += GND               # shield / mounting posts -> board GND
# link/act LEDs in the jack: anode -> 3V3 via R, cathode -> W5500 LED output (active low)
Rll = R('R4', '330R'); Rll[1] += P3V3; Rll[2] += J3['LEDGA']; J3['LEDGK'] += ETH_LL   # green = link
Ral = R('R5', '330R'); Ral[1] += P3V3; Ral[2] += J3['LEDYA']; J3['LEDYK'] += ETH_AL   # yellow = act

# ============================================================================
# U3  CH340K USB-UART (auto-reset)  + USB-C data inlet J2
# ============================================================================
CH = mk('CH340C', 'U', 'C84681:SOP-16_L10.0-W3.9-P1.27-LS6.0-BL',
        [(1, 'GND', PT.PWRIN), (2, 'TXD', PT.OUTPUT), (3, 'RXD', PT.INPUT), (4, 'V3', PT.PWROUT),
         (5, 'UDP', PT.PASSIVE), (6, 'UDM', PT.PASSIVE), (7, 'NC', PT.NOCONNECT), (8, 'OUT', PT.OUTPUT),
         (9, 'CTS', PT.INPUT), (10, 'DSR', PT.INPUT), (11, 'RI', PT.INPUT), (12, 'DCD', PT.INPUT),
         (13, 'DTR', PT.OUTPUT), (14, 'RTS', PT.OUTPUT), (15, 'R232', PT.INPUT), (16, 'VCC', PT.PWRIN)],
        value='CH340C')
U3 = CH(); U3.ref = 'U3'
U3['VCC'] += P3V3; U3['V3'] += P3V3; U3['GND'] += GND   # 3.3V operation: V3 tied to VCC (SOP-16, no EP)
U3['UDP'] += USB_DP; U3['UDM'] += USB_DM
U3['TXD'] += S3_RX; U3['RXD'] += S3_TX        # CH340 TXD -> S3 RX, CH340 RXD <- S3 TX
U3['DTR'] += DTR; U3['RTS'] += RTS
Cch = C('C15', '100nF'); Cch[1] += P3V3; Cch[2] += GND
# 2-transistor auto-reset (NodeMCU style): emitters cross to the opposite signal
NPN = mk('MMBT3904', 'Q', 'Package_TO_SOT_SMD:SOT-23',
         [(1, 'B', PT.INPUT), (2, 'E', PT.PASSIVE), (3, 'C', PT.OUTPUT)], value='MMBT3904')
Q1 = NPN(); Q1.ref = 'Q1'; Q2 = NPN(); Q2.ref = 'Q2'
Rq1 = R('R6', '10k'); Rq1[1] += RTS; Rq1[2] += Q1['B']; Q1['E'] += DTR; Q1['C'] += EN
Rq2 = R('R7', '10k'); Rq2[1] += DTR; Rq2[2] += Q2['B']; Q2['E'] += RTS; Q2['C'] += IO0

# USB-C (data) inlet
UC = mk('USB_C', 'J', 'C165948:USB-C_SMD-TYPE-C-31-M-12_1',
        [('A1B12', 'GND', PT.PASSIVE), ('B1A12', 'GND', PT.PASSIVE),
         ('A4B9', 'VBUS', PT.PASSIVE), ('B4A9', 'VBUS', PT.PASSIVE),
         ('A5', 'CC1', PT.PASSIVE), ('B5', 'CC2', PT.PASSIVE),
         ('A6', 'DP1', PT.PASSIVE), ('B6', 'DP2', PT.PASSIVE),
         ('A7', 'DN1', PT.PASSIVE), ('B7', 'DN2', PT.PASSIVE),
         ('A8', 'SBU1', PT.NOCONNECT), ('B8', 'SBU2', PT.NOCONNECT),
         (1, 'SH', PT.PASSIVE), (2, 'SH', PT.PASSIVE), (3, 'SH', PT.PASSIVE), (4, 'SH', PT.PASSIVE)],
        value='USB-C')
J2 = UC(); J2.ref = 'J2'
J2['VBUS'] += P5V_USB; J2['GND'] += GND   # USB 5V -> F1 fuse -> OR'd onto P5V via D8 (see PoE/OR section)
J2['DP1'] += USB_DP; J2['DP2'] += USB_DP; J2['DN1'] += USB_DM; J2['DN2'] += USB_DM
J2['CC1'] += CC1; J2['CC2'] += CC2
for p in (1, 2, 3, 4):
    J2[p] += GND          # shield
Rcc1 = R('R8', '5k1'); Rcc1[1] += CC1; Rcc1[2] += GND
Rcc2 = R('R9', '5k1'); Rcc2[1] += CC2; Rcc2[2] += GND
# USB input protection: F1 self-healing PTC fuse on VBUS + U8 USBLC6-2SC6 ESD/TVS array on D+/D-
PTC = mk('PPTC', 'F', 'Fuse:Fuse_1206_3216Metric', [(1, '1', PT.PASSIVE), (2, '2', PT.PASSIVE)],
         value='1.5A 16V PPTC')
F1 = PTC(); F1.ref = 'F1'; F1[1] += P5V_USB; F1[2] += P5V_USBF      # resettable overcurrent fuse (1.5A hold)
ESD = mk('USBLC6-2SC6', 'U', 'Package_TO_SOT_SMD:SOT-23-6',
         [(1, 'IO1', PT.PASSIVE), (2, 'GND', PT.PASSIVE), (3, 'IO2', PT.PASSIVE),
          (4, 'IO2', PT.PASSIVE), (5, 'VBUS', PT.PASSIVE), (6, 'IO1', PT.PASSIVE)], value='USBLC6-2SC6')
U8 = ESD(); U8.ref = 'U8'
U8[1] += USB_DP; U8[6] += USB_DP; U8[3] += USB_DM; U8[4] += USB_DM
U8[2] += GND; U8[5] += P5V_USB     # D+/D- ESD clamp to GND/VBUS; VBUS clamp taken at the connector (pre-fuse)

# ============================================================================
# PoE (IEEE 802.3af PD).  The HY931147C magjack (J3) rectifies PoE internally (Mode A+B)
#   and outputs DC on VPOE+/VPOE- -> DP9900M-5V isolated PD+DC-DC module -> +5V_POE.
#   The 37-57V rail (VPOE+/-) is isolated from board GND by the module (1.5 kV); its
#   -VDC becomes board GND.  +5V_POE is OR'd with USB 5V onto the +5V rail (D8/D9).
# ============================================================================
POE = mk('DP9900M-5V', 'U', 'C5380106:PWRM-SMD_DP9900M-5V',
         [(1, '+VDC', PT.PWROUT), (2, '+VDC', PT.PASSIVE), (3, '-VDC', PT.PWROUT), (4, 'ADJ', PT.PASSIVE),
          (5, 'VIN+', PT.PWRIN), (6, 'VIN+', PT.PASSIVE), (7, 'VIN-', PT.PWRIN), (8, 'VIN-', PT.PASSIVE)],
         value='DP9900M-5V')
U7 = POE(); U7.ref = 'U7'
U7[5] += VPOE_P; U7[6] += VPOE_P; U7[7] += VPOE_N; U7[8] += VPOE_N
U7[1] += P5V_POE; U7[2] += P5V_POE; U7[3] += GND   # isolated 5V out; -VDC -> board GND; ADJ(4) open = nominal 5V
TVSP = mk('SMAJ60A', 'D', 'Diode_SMD:D_SMA', [(1, 'K', PT.PASSIVE), (2, 'A', PT.PASSIVE)], value='SMAJ60A')
D10 = TVSP(); D10.ref = 'D10'; D10['K'] += VPOE_P; D10['A'] += VPOE_N   # rectified-PoE surge clamp: 60V standoff
# (was SMAJ58A: only 1V over the 57V PoE max -> nuisance leakage risk; SMAJ60A Vbr 66.7V, clamp ~96.8V)
Cpoe1 = C('C27', '100uF', 'Capacitor_SMD:CP_Elec_6.3x7.7'); Cpoe1[1] += P5V_POE; Cpoe1[2] += GND   # module output bulk (datasheet 100uF/25V)
Cpoe2 = C('C28', '10uF', 'Capacitor_SMD:C_0805_2012Metric'); Cpoe2[1] += P5V_POE; Cpoe2[2] += GND

# 5V source OR-ing via the TPS2116 ideal power-mux (replaces the SS54 OR diodes D8/D9). With MODE=GND and
# PR1=GND it automatically passes the HIGHER of VIN1 (fused USB) / VIN2 (PoE) to +5V, with reverse-current
# blocking (no backfeed). Rdson ~40mOhm -> ~32mV drop at 0.8A (vs ~0.4V for a Schottky), restoring the
# B0505S/ISO3086 VCC2 >=4.5V margin on USB power. LCSC C3235557, SOT-583 (8-pin). 1.6-5.5V in, 2.5A.
MUX = mk('TPS2116', 'U', 'Package_TO_SOT_SMD:SOT-583-8',
         [(1, 'GND', PT.PWRIN), (2, 'VOUT', PT.PWROUT), (3, 'VIN1', PT.PWRIN), (4, 'PR1', PT.INPUT),
          (5, 'MODE', PT.INPUT), (6, 'VIN2', PT.PWRIN), (7, 'VOUT', PT.PASSIVE), (8, 'ST', PT.PASSIVE)],
         value='TPS2116DRLR')
U9 = MUX(); U9.ref = 'U9'
U9['VIN1'] += P5V_USBF; U9['VIN2'] += P5V_POE; U9[2] += P5V; U9[7] += P5V; U9['GND'] += GND
U9['PR1'] += GND; U9['MODE'] += GND          # PR1=GND -> auto highest-voltage select; MODE=GND -> non-priority
# ST (pin 8) = open-drain status, left unconnected (optional 100k pull-up to +3V3 for a "which source" GPIO)
Cmuxa = C('C30', '1uF', 'Capacitor_SMD:C_0603_1608Metric'); Cmuxa[1] += P5V_USBF; Cmuxa[2] += GND  # TPS2116 VIN1 cap
Cmuxb = C('C31', '1uF', 'Capacitor_SMD:C_0603_1608Metric'); Cmuxb[1] += P5V_POE;  Cmuxb[2] += GND  # TPS2116 VIN2 cap
Cor = C('C29', '22uF', 'Capacitor_SMD:C_0805_2012Metric'); Cor[1] += P5V; Cor[2] += GND
# +5V rail transient clamp (D11) + EMC ferrite (FB1) feeding the isolated DMX DC-DC inputs
TVS5 = mk('SMAJ5.0A', 'D', 'Diode_SMD:D_SMA', [(1, 'K', PT.PASSIVE), (2, 'A', PT.PASSIVE)], value='SMAJ5.0A')
D11 = TVS5(); D11.ref = 'D11'; D11['K'] += P5V; D11['A'] += GND
FBEAD = mk('FerriteBead', 'FB', 'Inductor_SMD:L_0805_2012Metric',
           [(1, '1', PT.PASSIVE), (2, '2', PT.PASSIVE)], value='600R@100MHz')
FB1 = FBEAD(); FB1.ref = 'FB1'; FB1[1] += P5V; FB1[2] += P5V_DMX   # input filter for PS1/PS2 (DMX iso DC-DCs)

# ============================================================================
# U4  SY8089 5V -> 3.3V buck
# ============================================================================
BK = mk('SY8089', 'U', 'C78988:SOT-23-5_L3.0-W1.7-P0.95-LS2.8-BR',
        [(1, 'EN', PT.INPUT), (2, 'GND', PT.PWRIN), (3, 'LX', PT.OUTPUT), (4, 'IN', PT.PWRIN), (5, 'FB', PT.INPUT)],
        value='SY8089')
U4 = BK(); U4.ref = 'U4'
U4['IN'] += P5V; U4['EN'] += P5V; U4['GND'] += GND; U4['LX'] += LX; U4['FB'] += FB
L1 = mk('L', 'L', 'C354584:IND-SMD_L4.0-W4.0', [(1, '1', PT.PASSIVE), (2, '2', PT.PASSIVE)], value='2.2uH')()
L1.ref = 'L1'; L1[1] += LX; L1[2] += P3V3
Cin = C('C16', '22uF', 'Capacitor_SMD:C_0805_2012Metric'); Cin[1] += P5V; Cin[2] += GND
Cout = C('C17', '22uF', 'Capacitor_SMD:C_0805_2012Metric'); Cout[1] += P3V3; Cout[2] += GND
Rfb1 = R('R10', '45.3k'); Rfb1[1] += P3V3; Rfb1[2] += FB     # FB divider: 0.6*(1+45.3/10)=3.32V (YAGEO RC0402FR-0745K3L / C137977)
Rfb2 = R('R11', '10k'); Rfb2[1] += FB; Rfb2[2] += GND

# ============================================================================
# Isolated DMX:  U5 ISO3086DWR (iso RS-485) + PS1 B0505S iso-DCDC + J1 XLR-3 + protection
# ============================================================================
ISO = mk('ISO3086DWR', 'U', 'C183095:SOIC-16_L10.3-W7.5-P1.27-LS10.3-BL',
         [(1, 'VCC1', PT.PWRIN), (2, 'GND1', PT.PWRIN), (3, 'R', PT.OUTPUT), (4, 'nRE', PT.INPUT),
          (5, 'DE', PT.INPUT), (6, 'D', PT.INPUT), (7, 'GND1', PT.PWRIN), (8, 'GND1', PT.PWRIN),
          (9, 'GND2', PT.PWRIN), (10, 'GND2', PT.PWRIN), (11, 'Y', PT.OUTPUT), (12, 'Z', PT.OUTPUT),
          (13, 'B', PT.BIDIR), (14, 'A', PT.BIDIR), (15, 'GND2', PT.PWRIN), (16, 'VCC2', PT.PWRIN)],
         value='ISO3086DWR')
U5 = ISO(); U5.ref = 'U5'
U5['VCC1'] += P3V3; U5[2] += GND; U5[7] += GND; U5[8] += GND
U5['R'] += DMX_RX; U5['D'] += DMX_TX; U5['nRE'] += DMX_EN; U5['DE'] += DMX_EN
# NB: a 10k pull-down on DMX_EN (and DMX2_EN below) would hold the ISO3086 drivers OFF while IO8/IO47 are
# high-Z during ESP32 boot (avoids a brief indeterminate DMX drive). Evaluated but NOT fitted: adding the
# two resistors forces the W5500 Ethernet TX diff-pair to take a via, hurting 100BASE-TX SI. Next-spin item.
U5['VCC2'] += VISO_DRV; U5[9] += GND2; U5[10] += GND2; U5[15] += GND2
U5['Y'] += DMX_A; U5['A'] += DMX_A; U5['Z'] += DMX_B; U5['B'] += DMX_B   # 2-wire: Y-A=Data+, Z-B=Data-
Ciso1 = C('C18', '100nF'); Ciso1[1] += P3V3; Ciso1[2] += GND
Ciso2 = C('C19', '100nF'); Ciso2[1] += VISO_DRV; Ciso2[2] += GND2       # driver-local decouple (after FB2)
Ciso3 = C('C20', '10uF', 'Capacitor_SMD:C_1206_3216Metric'); Ciso3[1] += VISO; Ciso3[2] += GND2  # DC-DC output bulk
FB2 = FBEAD(); FB2.ref = 'FB2'; FB2[1] += VISO; FB2[2] += VISO_DRV      # keeps DC-DC switching noise off the DMX driver

PSU = mk('B0505S-1W', 'PS', 'C2912568:PWRM-TH_B0505S-1W',
         [(1, 'GNDin', PT.PWRIN), (2, 'VIN', PT.PWRIN), (3, 'GNDout', PT.PWROUT), (4, 'VOUT', PT.PWROUT)],
         value='B0505S-1W')
PS1 = PSU(); PS1.ref = 'PS1'
PS1['VIN'] += P5V_DMX; PS1['GNDin'] += GND; PS1['VOUT'] += VISO; PS1['GNDout'] += GND2
Cb = C('C21', '10uF', 'Capacitor_SMD:C_1206_3216Metric'); Cb[1] += P5V_DMX; Cb[2] += GND

# DMX termination (at the transceiver) + L2 common-mode choke + TVS clamp (at the cable) + XLR-5
Rterm = R('R12', '120R', 'Resistor_SMD:R_0805_2012Metric'); Rterm[1] += DMX_A; Rterm[2] += DMX_B
# Fail-safe BIAS (RDM idle): pull DMX_A up to the isolated 5V (VISO_DRV) and DMX_B down to GND2, on the
# ISOLATED side. ~470R holds the idle differential >=~250mV even worst-case (both ends terminated -> 60R,
# VISO=5V: 5*60/(60+2*470)=300mV), so the ISO3086 receiver reads a defined MARK when the bus is undriven
# during the RDM turnaround (no bias = floating idle line = the 36% framing errors seen on the breadboard
# rig). ~5mA/universe, the B0505S shrugs it off. Not an E1.11 requirement; an RDM-receive robustness add.
Rb1a = R('R20', '470R'); Rb1a[1] += DMX_A; Rb1a[2] += VISO_DRV
Rb1b = R('R21', '470R'); Rb1b[1] += DMX_B; Rb1b[2] += GND2
CMC = mk('ACM2012-201-2P', 'L', 'Inductor_SMD:L_CommonModeChoke_Coilank_ACM2012',
         [(1, '1', PT.PASSIVE), (2, '2', PT.PASSIVE), (3, '3', PT.PASSIVE), (4, '4', PT.PASSIVE)],
         value='ACM2012-201-2P')
L2 = CMC(); L2.ref = 'L2'
L2[1] += DMX_A; L2[4] += DMX_AO; L2[2] += DMX_B; L2[3] += DMX_BO   # windings A:1-4, B:2-3 (in=left 1/2, out=right 4/3)
TVS = mk('SM712', 'D', 'Package_TO_SOT_SMD:SOT-23',
         [(1, 'IO1', PT.PASSIVE), (2, 'GND', PT.PASSIVE), (3, 'IO2', PT.PASSIVE)], value='SM712')
D1 = TVS(); D1.ref = 'D1'; D1['IO1'] += DMX_AO; D1['GND'] += GND2; D1['IO2'] += DMX_BO   # clamp (transceiver side of the TBU)
# DMX512-A Protected (Annex C): series TBU high-speed protector per data line, between the XLR/cable (DMX_*X)
# and the SM712/choke node (DMX_*O). Bourns TBU-CA065-200-WH (C913221): bidirectional electronic current
# limiter, 200mA hold / 650V standoff / 8.6R / <1us response. On a sustained 30VAC/42VDC fault the current
# rises and the TBU TRIGGERS in <1us, going high-Z and BLOCKING the fault (holds off up to 650V); the SM712
# then only sees the sub-us trigger transient (exactly its 8/20us job) -- no sustained current, nothing
# overheats. Self-resets when the fault clears. This is why the TBU replaces the slow PTC: the 1.5R PTC let
# ~19A through the SM712 for ms before its thermal trip; the TBU blocks before the SM712 can overheat (the
# standard's named "fault-protected" approach). Pin 1/3 = the two terminals (bidirectional, interchangeable),
# pin 2 = NU (not used, left unconnected). 8.6R x2 series is signal-OK: ~1.75V at the far receiver (8.7x the
# 200mV threshold), RDM near-end reflection ~6.6%. I_op 200mA vs ~50mA DMX peak = 4x no-nuisance-trip margin.
TBU = mk('TBU-CA065-200-WH', 'F', 'C913221:DIO-SMD_3P-L6.5-W4.0-BI',
         [(1, 'IN/OUT', PT.PASSIVE), (2, 'NU', PT.NOCONNECT), (3, 'OUT/IN', PT.PASSIVE)], value='TBU 200mA 650V')
F2 = TBU(); F2.ref = 'F2'; F2[1] += DMX_AX; F2[3] += DMX_AO   # DMX1 Data+ protect (pin2 NU unconnected)
F3 = TBU(); F3.ref = 'F3'; F3[1] += DMX_BX; F3[3] += DMX_BO   # DMX1 Data- protect
# 5-pin XLR (E1.11/DMX512-A): Neutrik NC5FAH (C368501) -- female, horizontal THT PCB mount.
#   1=shield/common 2=Data1- 3=Data1+; 4/5 = optional 2nd data link, NC for one driver per port.
#   G/6/7 = shell + mounting posts -> tied to the isolated DMX ground.
XLR = mk('NC5FAH', 'J', 'C368501:CONN-TH_NC5FAH',
         [(1, 'SHIELD', PT.PASSIVE), (2, 'DATA-', PT.PASSIVE), (3, 'DATA+', PT.PASSIVE),
          (4, 'NC4', PT.NOCONNECT), (5, 'NC5', PT.NOCONNECT),
          ('G', 'SHELL', PT.PASSIVE), (6, 'SHELL6', PT.PASSIVE), (7, 'SHELL7', PT.PASSIVE)],
         value='XLR-5 NC5FAH')
J1 = XLR(); J1.ref = 'J1'
J1['SHIELD'] += GND2; J1['SHELL'] += GND2; J1[6] += GND2; J1[7] += GND2
J1['DATA-'] += DMX_BX; J1['DATA+'] += DMX_AX   # cable side of the F2/F3 PTC (Protected)

# ============================================================================
# Isolated DMX universe 2:  U6 ISO3086DWR + PS2 B0505S iso-DCDC + J5 XLR-3 + protection
#   fully independent galvanic island (VISO2 / GNDISO2); driven on UART/port 2
#   (S3: D=IO16, R=IO21, DE/nRE=IO47).  Mirror of universe 1 (U5/PS1/J1).
# ============================================================================
U6 = ISO(); U6.ref = 'U6'
U6['VCC1'] += P3V3; U6[2] += GND; U6[7] += GND; U6[8] += GND
U6['R'] += DMX2_RX; U6['D'] += DMX2_TX; U6['nRE'] += DMX2_EN; U6['DE'] += DMX2_EN
U6['VCC2'] += VISO2_DRV; U6[9] += GNDI2; U6[10] += GNDI2; U6[15] += GNDI2
U6['Y'] += DMX2_A; U6['A'] += DMX2_A; U6['Z'] += DMX2_B; U6['B'] += DMX2_B   # 2-wire: Y-A=Data+, Z-B=Data-
Ciso4 = C('C23', '100nF'); Ciso4[1] += P3V3;  Ciso4[2] += GND
Ciso5 = C('C24', '100nF'); Ciso5[1] += VISO2_DRV; Ciso5[2] += GNDI2     # driver-local decouple (after FB3)
Ciso6 = C('C25', '10uF', 'Capacitor_SMD:C_1206_3216Metric'); Ciso6[1] += VISO2; Ciso6[2] += GNDI2  # DC-DC output bulk
FB3 = FBEAD(); FB3.ref = 'FB3'; FB3[1] += VISO2; FB3[2] += VISO2_DRV

PS2 = PSU(); PS2.ref = 'PS2'
PS2['VIN'] += P5V_DMX; PS2['GNDin'] += GND; PS2['VOUT'] += VISO2; PS2['GNDout'] += GNDI2
Cb2 = C('C26', '10uF', 'Capacitor_SMD:C_1206_3216Metric'); Cb2[1] += P5V_DMX; Cb2[2] += GND

# DMX2 termination + L3 common-mode choke + TVS clamp (at the cable) + XLR-5
Rterm2 = R('R19', '120R', 'Resistor_SMD:R_0805_2012Metric'); Rterm2[1] += DMX2_A; Rterm2[2] += DMX2_B
# Fail-safe BIAS for universe 2 (mirror of R20/R21, on the VISO2/GNDISO2 island)
Rb2a = R('R22', '470R'); Rb2a[1] += DMX2_A; Rb2a[2] += VISO2_DRV
Rb2b = R('R23', '470R'); Rb2b[1] += DMX2_B; Rb2b[2] += GNDI2
L3 = CMC(); L3.ref = 'L3'
L3[1] += DMX2_A; L3[4] += DMX2_AO; L3[2] += DMX2_B; L3[3] += DMX2_BO   # windings A:1-4, B:2-3
D7 = TVS(); D7.ref = 'D7'; D7['IO1'] += DMX2_AO; D7['GND'] += GNDI2; D7['IO2'] += DMX2_BO   # clamp (transceiver side of the TBU)
# DMX512-A Protected universe 2: series TBU F4/F5 (mirror of F2/F3), DMX2_*X -> TBU -> DMX2_*O
F4 = TBU(); F4.ref = 'F4'; F4[1] += DMX2_AX; F4[3] += DMX2_AO   # DMX2 Data+ protect (pin2 NU unconnected)
F5 = TBU(); F5.ref = 'F5'; F5[1] += DMX2_BX; F5[3] += DMX2_BO   # DMX2 Data- protect
J5 = XLR(); J5.ref = 'J5'
J5['SHIELD'] += GNDI2; J5['SHELL'] += GNDI2; J5[6] += GNDI2; J5[7] += GNDI2
J5['DATA-'] += DMX2_BX; J5['DATA+'] += DMX2_AX   # cable side of the F4/F5 PTC (Protected)

# ============================================================================
# Status LEDs (direct on S3 GPIOs): GPIO -> R -> LED anode, cathode -> GND
# ============================================================================
LEDP = mk('LED', 'D', 'LED_SMD:LED_0603_1608Metric',
          [(1, 'K', PT.PASSIVE), (2, 'A', PT.PASSIVE)], value='LED')
for ref, net, rref, rval in [('D2', LED_R, 'R13', '1k'), ('D3', LED_G, 'R14', '150R'),
                             ('D4', LED_Y, 'R15', '1k'), ('D5', LED_B, 'R16', '150R'),
                             ('D6', LED_W, 'R17', '150R')]:
    d = LEDP(); d.ref = ref
    r = R(rref, rval)
    r[1] += net; r[2] += d['A']; d['K'] += GND

# ============================================================================
# J4  Display breakout header (optional OLED/TFT status panel — issue #5, docs/display.md)
#   I2C mono OLED (SSD1306/SH1106): SDA=IO4  SCL=IO5
#   color SPI OLED/TFT (SSD1351/ST7789): SCK=IO39 MOSI=IO40 CS=IO41 DC=IO42 RST=IO38
#   NB: v3 uses these FREE GPIOs, NOT the doc's S3 default 8/9 (here 8=DMX_DE, 9=ETH_RST).
#   Firmware must set dispSda/dispScl (+ SPI pins) in /config to match this header.
# ============================================================================
DISP_SDA = Net('DISP_SDA'); DISP_SCL = Net('DISP_SCL')
DISP_SCK = Net('DISP_SCK'); DISP_MOSI = Net('DISP_MOSI'); DISP_CS = Net('DISP_CS')
DISP_DC  = Net('DISP_DC');  DISP_RST  = Net('DISP_RST')
U1['IO4']  += DISP_SDA;  U1['IO5']  += DISP_SCL
U1['IO39'] += DISP_SCK;  U1['IO40'] += DISP_MOSI; U1['IO41'] += DISP_CS
U1['IO42'] += DISP_DC;   U1['IO38'] += DISP_RST
HDR = mk('Conn_JSTSH9', 'J', 'Connector_JST:JST_SH_SM09B-SRSS-TB_1x09-1MP_P1.00mm_Horizontal',
         [(i, str(i), PT.PASSIVE) for i in range(1, 10)] + [('MP', 'MP', PT.PASSIVE)], value='DISP SH9')
J4 = HDR(); J4.ref = 'J4'
# JST SH 1.0mm 9-pin SMD side-entry (~10mm wide; pre-crimped cables available):
#   1 +3V3  2 GND  3 SDA  4 SCL  5 SCK  6 MOSI  7 CS  8 DC  9 RST
J4[1] += P3V3;      J4[2] += GND;       J4[3] += DISP_SDA; J4[4] += DISP_SCL; J4[5] += DISP_SCK
J4[6] += DISP_MOSI; J4[7] += DISP_CS;   J4[8] += DISP_DC;  J4[9] += DISP_RST
J4['MP'] += GND     # mounting tabs -> GND (mechanical anchor + shield)

# ============================================================================
# J6  Expansion header (JST SH 1.0mm 9-pin) — breaks out 6 FREE, non-strapping
#   ESP32-S3 GPIOs + power for I2C / SPI / UART / GPIO add-ons.
#     1 +5V  2 +3V3  3 GND  4 IO35  5 IO36  6 IO37  7 IO48  8 IO19  9 IO20
#   Any pin muxes to I2C (SDA/SCL), SPI (SCK/MOSI/MISO/CS), UART, PWM or ADC in
#   firmware, so the port can run an I2C bus AND a SPI bus at once. IO19/IO20 are
#   also the S3 native-USB D-/D+ (free here because USB-UART is the CH340).
# ============================================================================
EXP35 = Net('EXP_IO35'); EXP36 = Net('EXP_IO36'); EXP37 = Net('EXP_IO37')
EXP48 = Net('EXP_IO48'); EXP19 = Net('EXP_IO19'); EXP20 = Net('EXP_IO20')
U1['IO35'] += EXP35; U1['IO36'] += EXP36; U1['IO37'] += EXP37
U1['IO48'] += EXP48; U1['IO19'] += EXP19; U1['IO20'] += EXP20
J6 = HDR(); J6.ref = 'J6'; J6.value = 'EXP SH9'
J6[1] += P5V;   J6[2] += P3V3;  J6[3] += GND
J6[4] += EXP35; J6[5] += EXP36; J6[6] += EXP37
J6[7] += EXP48; J6[8] += EXP19; J6[9] += EXP20
J6['MP'] += GND

# ============================================================================
# J7 / J8  DMX-output breakout headers (JST SH 1.0mm 3-pin) — in PARALLEL with the
#   XLRs J1/J5. Depopulate the on-board XLR and wire an external panel connector via
#   the header instead (or fit both). Same ISOLATED nets, pinout mirrors the XLR:
#     1 = Shield/common (GNDISO)   2 = Data-   3 = Data+
#   MUST stay inside the isolated DMX region (>=4mm from board GND) like the XLR.
# ============================================================================
SH3 = mk('Conn_JSTSH3', 'J', 'Connector_JST:JST_SH_SM03B-SRSS-TB_1x03-1MP_P1.00mm_Horizontal',
         [(1, '1', PT.PASSIVE), (2, '2', PT.PASSIVE), (3, '3', PT.PASSIVE), ('MP', 'MP', PT.PASSIVE)],
         value='DMX SH3')
J7 = SH3(); J7.ref = 'J7'; J7.value = 'DMX-OUT A'
J7[1] += GND2;  J7[2] += DMX_BX;  J7[3] += DMX_AX;  J7['MP'] += GND2   # cable side of the PTC
J8 = SH3(); J8.ref = 'J8'; J8.value = 'DMX-OUT B'
J8[1] += GNDI2; J8[2] += DMX2_BX; J8[3] += DMX2_AX; J8['MP'] += GNDI2   # cable side of the PTC

# ============================================================================
# Mounting holes — PLATED M3, tied to board GND. The 4 corners bond the DIGITAL ground
#   to a metal chassis at multiple points (multipoint HF grounding: the case becomes a
#   shield referenced to GND, so common-mode currents from Ethernet/USB/the switchers
#   return to chassis locally instead of looping the board). The ISOLATED DMX grounds
#   stay OFF chassis (isolating XLR mounting). set_outline_holes.py places these at the
#   4 symmetric corners. See docs/ruggedization.md "Grounding & shielding".
# ============================================================================
MHP = mk('MountingHole', 'MH', 'MountingHole:MountingHole_3.2mm_M3_Pad',
         [(1, '1', PT.PASSIVE)], value='M3 GND')
for _i in range(1, 5):
    _mh = MHP(); _mh.ref = f'MH{_i}'; _mh[1] += GND

# ============================================================================
# Soft-ground bridge (GNDISO/GNDISO2 -> GND/chassis via 1nF + 1M, per universe) was
# evaluated here but NOT fitted: on this tightly-packed board the bridge has to cross the
# 4mm isolation void right at the congested PS1/PS2 barrier, which either pushes the void
# into the adjacent board-GND parts or strands the barrier GND/+3V3 routing. The DMX cable
# shield is instead referenced at the console end + the isolating XLR mount keeps the port
# floating; see docs/ruggedization.md "Grounding & shielding" for the soft-ground option if
# the layout is ever loosened. (Pads/refs C30/C31/R20/R21 reserved for that.)
# ============================================================================

ERC()
generate_netlist(file_=os.path.join(HERE, 'luxdmx.net'))
print('NETLIST GENERATED OK ->', os.path.join(HERE, 'luxdmx.net'))
